andreabenini/controlpad/electronics/controlpad/controlpad.kicad_sch

## KiCad design electronics/controlpad/controlpad.kicad_sch (2025-04-29, an earlier design)

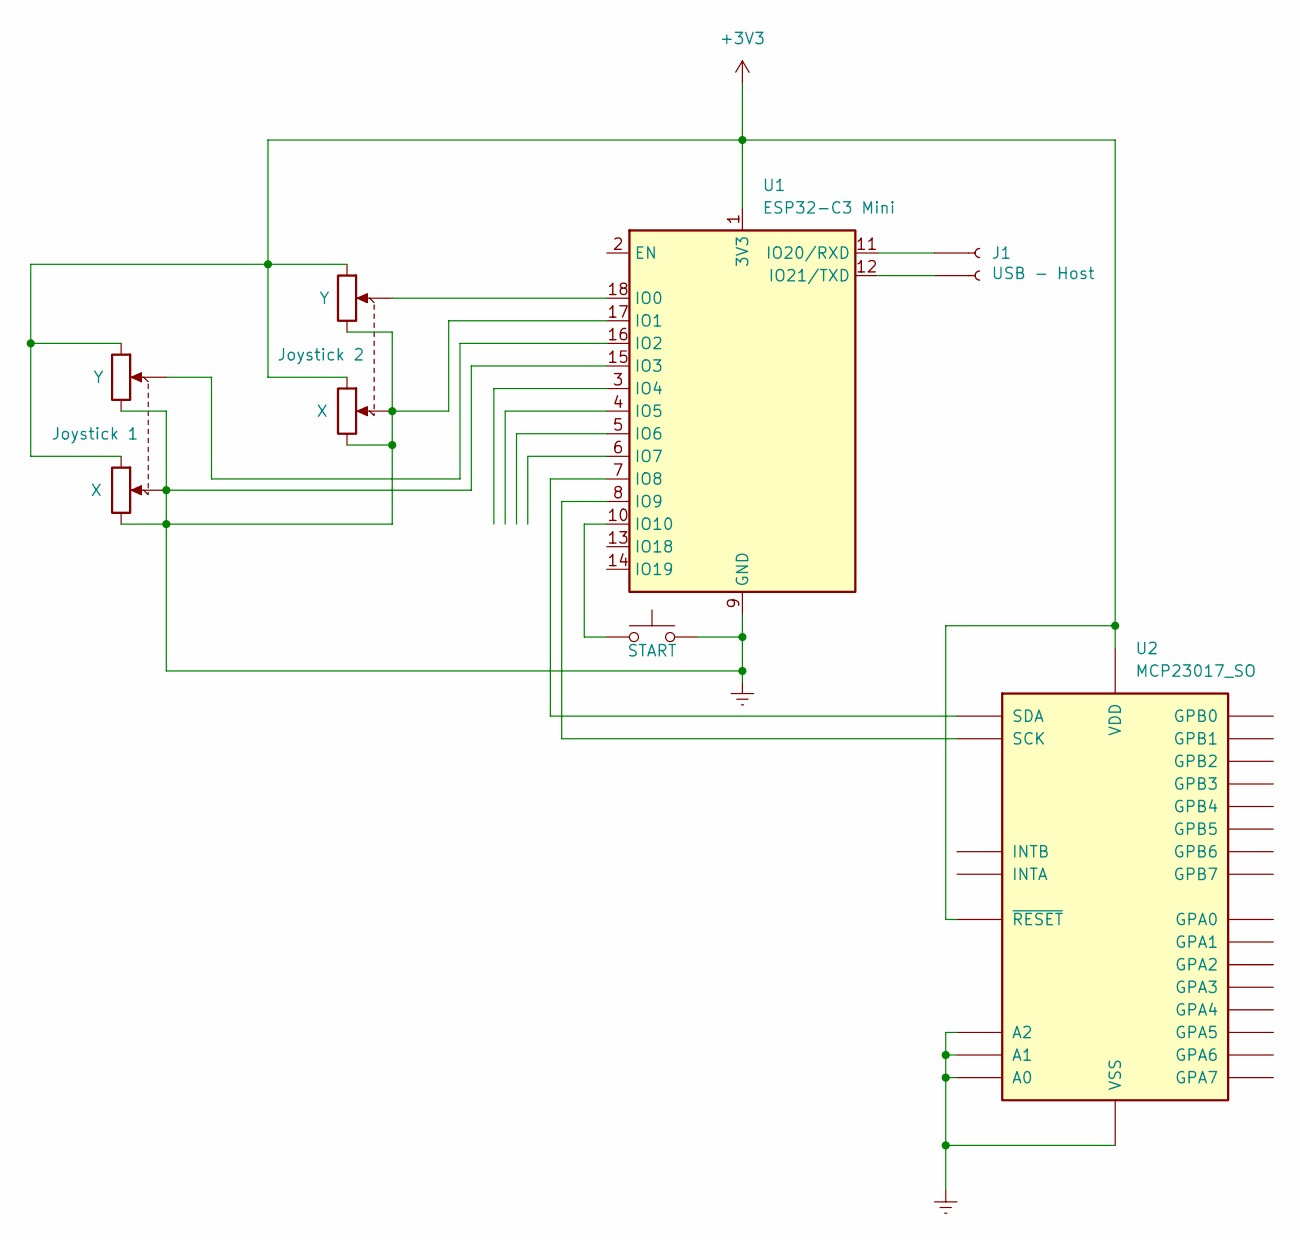
[picture p9: schematic controlpad.kicad_sch]

Parts:
J1: USB - Host
RV1: Joystick 2
RV2: Joystick 1
SW1: START
U1: ESP32-C3 Mini; ESP32-C3-WROOM-02
U2: MCP23017_SO; SOIC-28W_7.5x17.9mm_P1.27mm

Connections:
+3V3: RV1.1, RV1.4, RV2.1, RV2.4, U1.1 (3V3), U2.9 (VDD), U2.18 (~RESET)
GNDREF: RV1.3, RV1.5, RV1.6, RV2.3, RV2.5, RV2.6, SW1.2, U1.9 (GND), U1.15 (IO3), U1.17 (IO1), U1.19 (GND), U2.10 (VSS), U2.15 (A0), U2.16 (A1), U2.17 (A2)
unnamed: J1.1, U1.11 (IO20/RXD)
unnamed: J1.2, U1.12 (IO21/TXD)
unnamed: RV1.2, U1.18 (IO0)
unnamed: RV2.2, U1.16 (IO2)
unnamed: SW1.1, U1.10 (IO10)
unnamed: U1.7 (IO8), U2.13 (SDA)
unnamed: U1.8 (IO9), U2.12 (SCK)
