andreabenini/controlpad/software/main/joystick.h

#ifndef JOYSTICK__H
#define JOYSTICK__H


#include "freertos/FreeRTOS.h"                                  // IWYU pragma: keep
#include "driver/i2c_master.h"                                  // IWYU pragma: keep
#include "esp_adc/adc_continuous.h"
#include <esp_err.h>
#include <esp_log.h>


// Joysticks initialization
esp_err_t joystickInit(adc_channel_t (*channel)[4], adc_continuous_handle_t *adcHandle);


#endif
